PiotrKnutel/rejestrator_parametrow_srodowiskowych/zdjęcia/P1070148.JPG

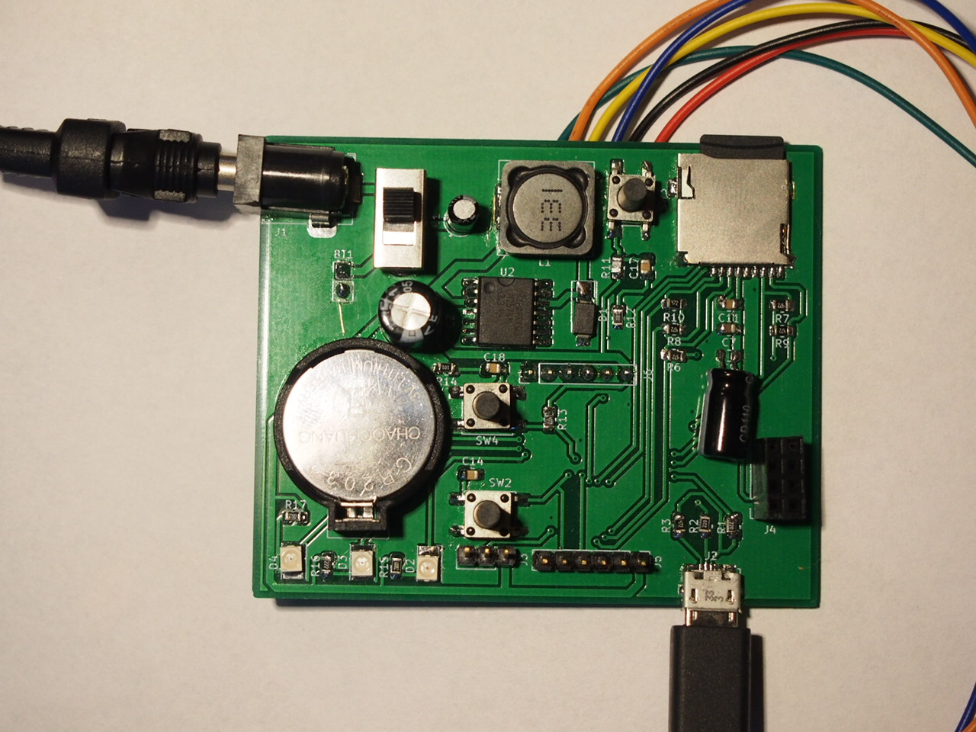
zdjęcia/P1070148.JPG
