PiotrKnutel/rejestrator_parametrow_srodowiskowych/zdjęcia/P1070149.JPG

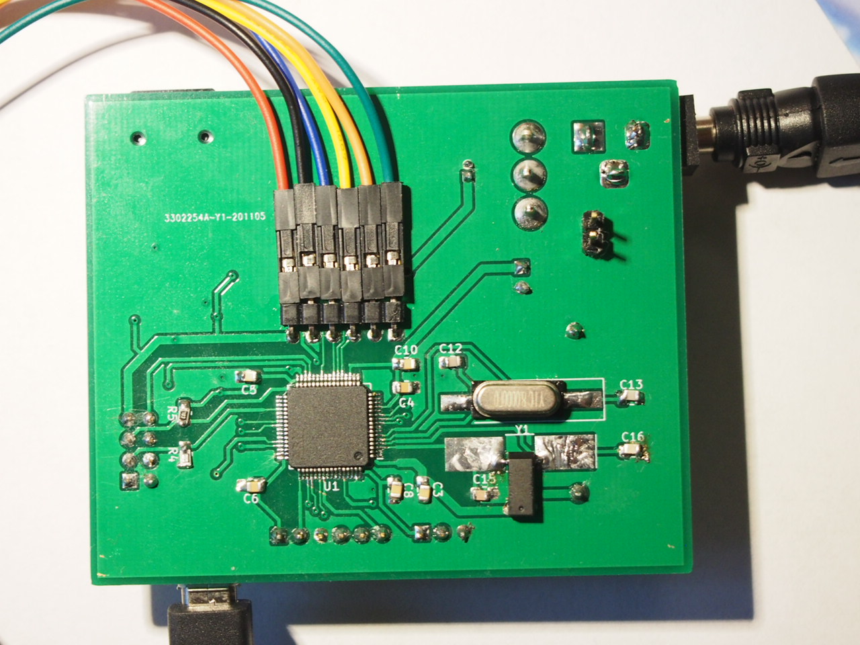
zdjęcia/P1070149.JPG
