PiotrKnutel/rejestrator_parametrow_srodowiskowych/zdjęcia/P1070150.JPG

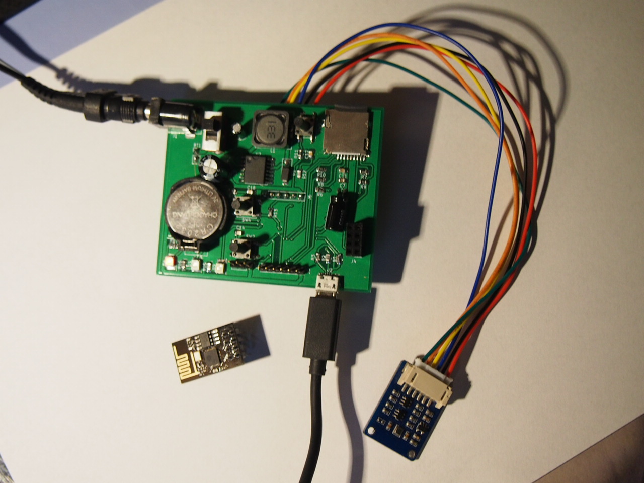
zdjęcia/P1070150.JPG
