PiotrKnutel/rejestrator_parametrow_srodowiskowych/zdjęcia/P2128904.JPG

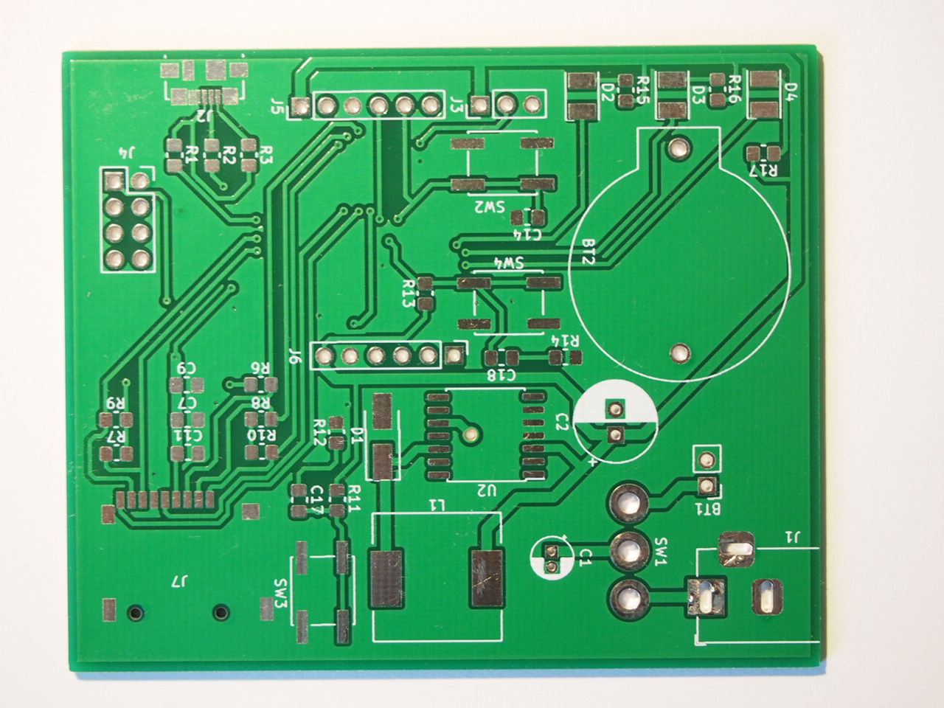
zdjęcia/P2128904.JPG
