PiotrKnutel/rejestrator_parametrow_srodowiskowych/zdjęcia/P2128905.JPG

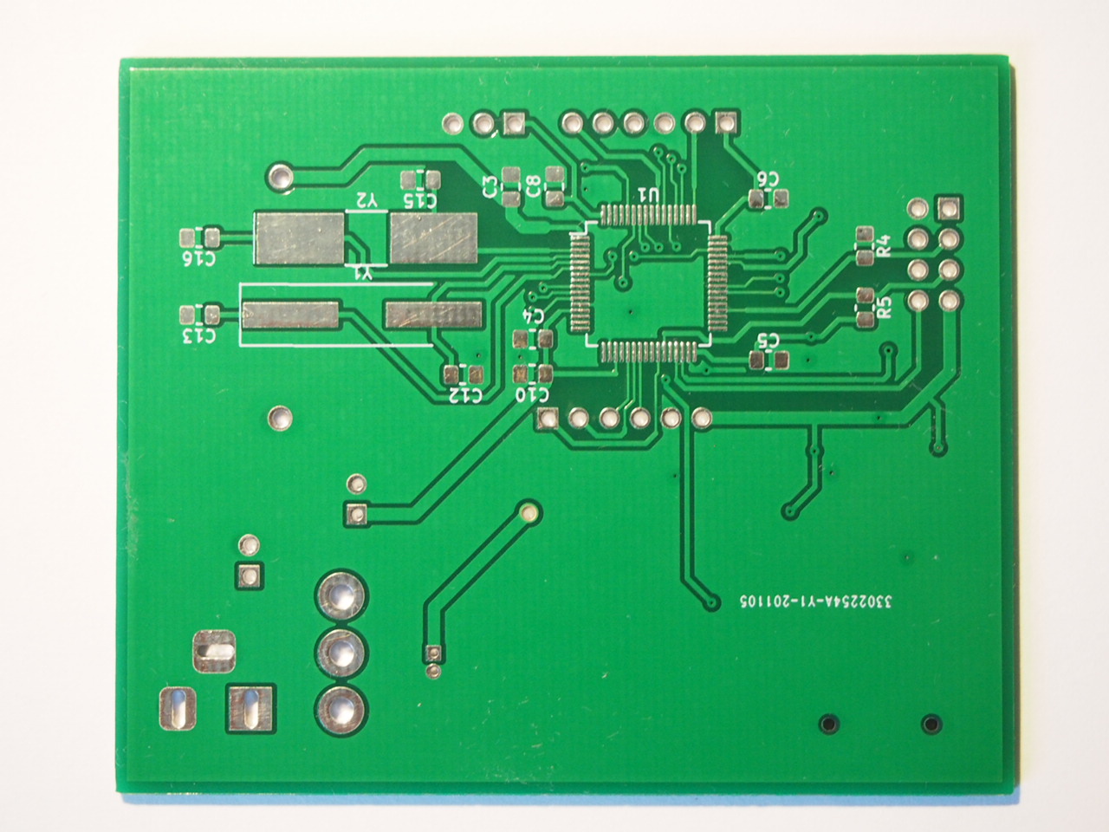
zdjęcia/P2128905.JPG
